TeamRAISE/RAISE/STL/Gridfinity/Baseplate_1-4.STL

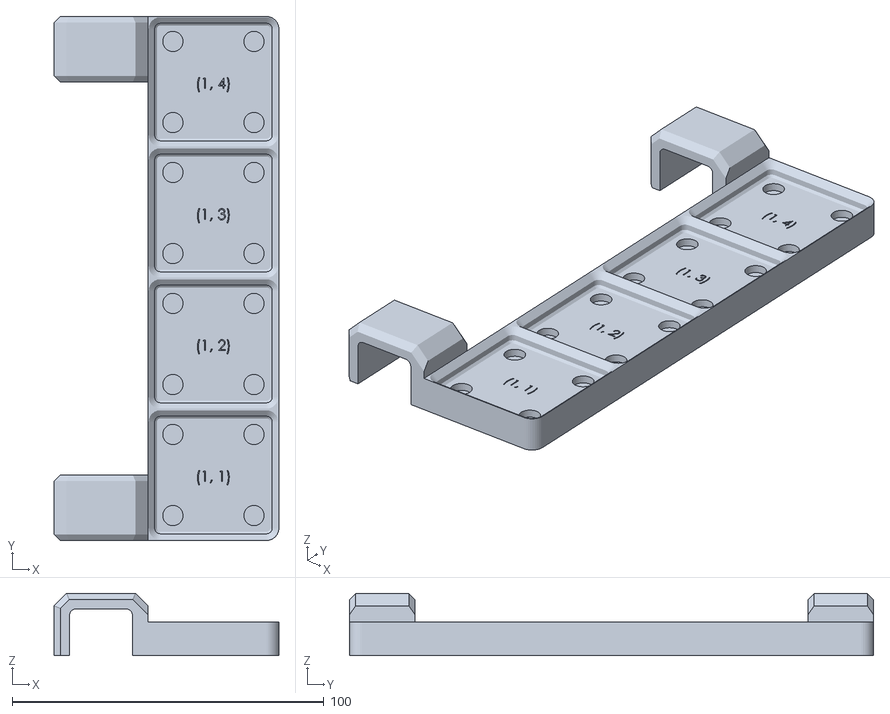
[picture p19: CAD file, 2025-06-04]
STL/Gridfinity/Baseplate_1-4.STL
72.1 x 168.0 x 20.0
