TeamRAISE/RAISE/CAD/Scooter_Klemme_x4.STEP

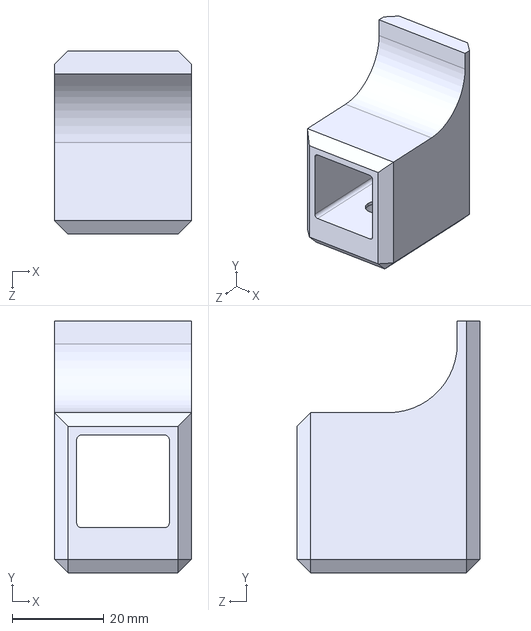
[picture p20: CAD file, 2025-06-04]
CAD/Scooter_Klemme_x4.STEP
30.0 x 55.0 x 40.0 mm
